oms9/MacropadV4/CAD - MacropadV4/STLs/Macropadv4-Shell.STL

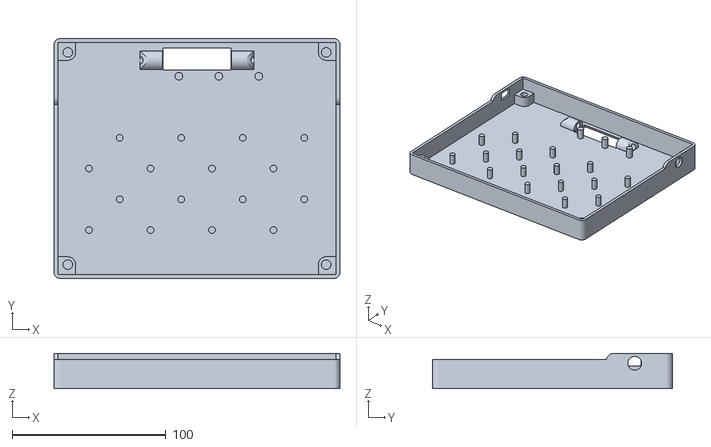
[picture p16: CAD file, 2024-06-29]
CAD - MacropadV4/STLs/Macropadv4-Shell.STL
186.0 x 156.0 x 23.0
