oms9/MacropadV4/CAD - MacropadV4/parts/旋转编码器.SLDPRT

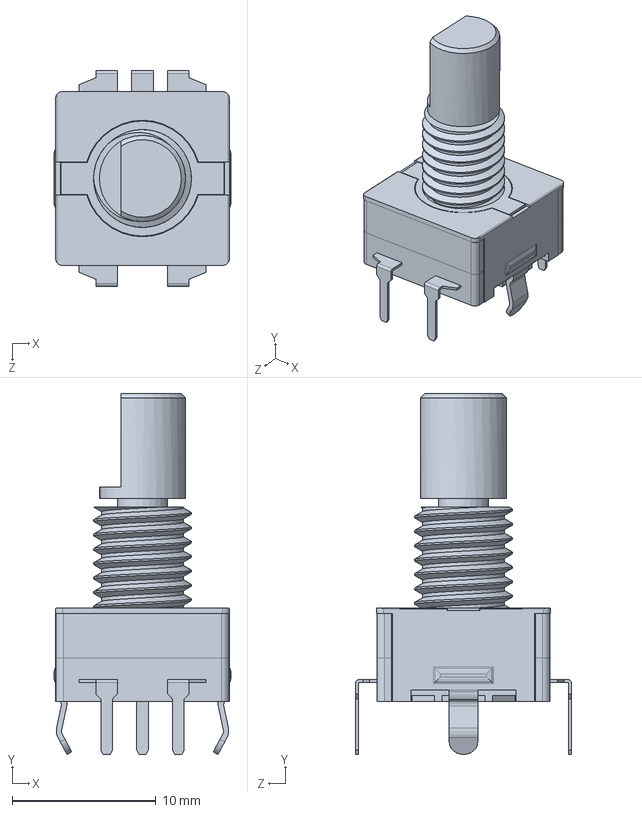
[picture p17: CAD file, 2024-06-29]
CAD - MacropadV4/parts/旋转编码器.SLDPRT
12.3 x 25.1 x 15.0 mm
